lopsided98/zeus-le/pcb/sim/decoupling_resonance.asc

I1: current; 12m
L1: ind; 12n; Rser=0
L2: ind; 0; Rser=0
U1: CL05A104KA5NNN_Precise_Interactive_LT
U3: GRM188R61A106ME69_LT
V1: voltage; SINE(3.2 1 30k); AC 1; Rser=0.
Named nets: 0
.ac dec 100 10 100Meg
