lopsided98/zeus-le/pcb/sim/vdda_filter.asc

C3: cap; 0.1µ; Irms=0 Rser=0 Lser=0 Rpar=0 Cpar=0
I1: current; 14m
L1: ind; 10n; Rser=0 Rpar=0 Cpar=0
L3: ind; 16n; Rser=0 Rpar=0 Cpar=0
R1: res; 0.1
R2: res; 0.013
R3: res; 0.0082
U1: CL10B105KP8NNN_Precise_Interactive_LT
U2: MLZ2012N220LT000_b
U3: CL31A107MQHNNW_Precise_Interactive_LT
V1: voltage; SINE(0 50m 100k); AC 1
Named nets: 0, VDDA
.ac dec 100 100 10Meg
.meas AC VDDA_PEAK MAX V(vdda) from 0 to 1meg
.meas AC VDDA_30k FIND V(vdda) AT 30k
